topolittle/rx8-coolant-monitor/MECHA/Head_Unit/STEP/Head_Unit_cutting_jig.STEP

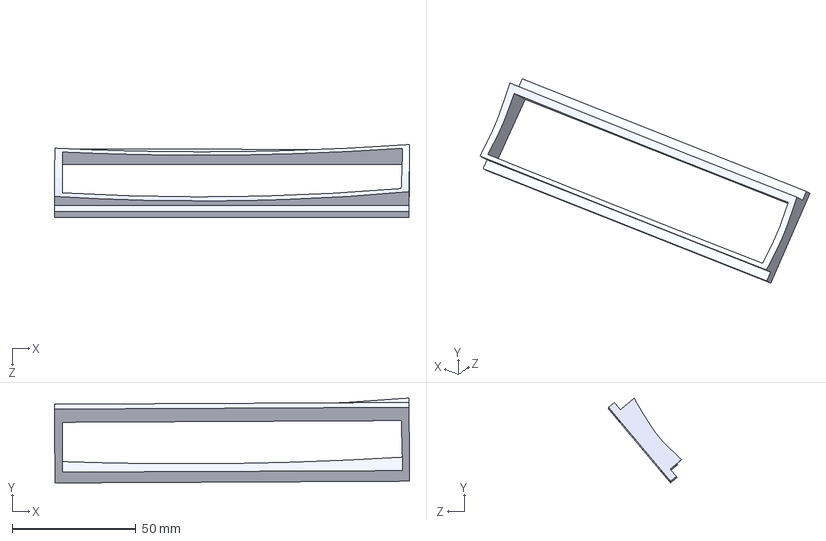
[picture p23: CAD file, 2022-10-16]
MECHA/Head_Unit/STEP/Head_Unit_cutting_jig.STEP
143.4 x 34.3 x 29.4 mm
