topolittle/rx8-coolant-monitor/MECHA/Controller_Enclosure/Solidworks/1723162108.SLDPRT

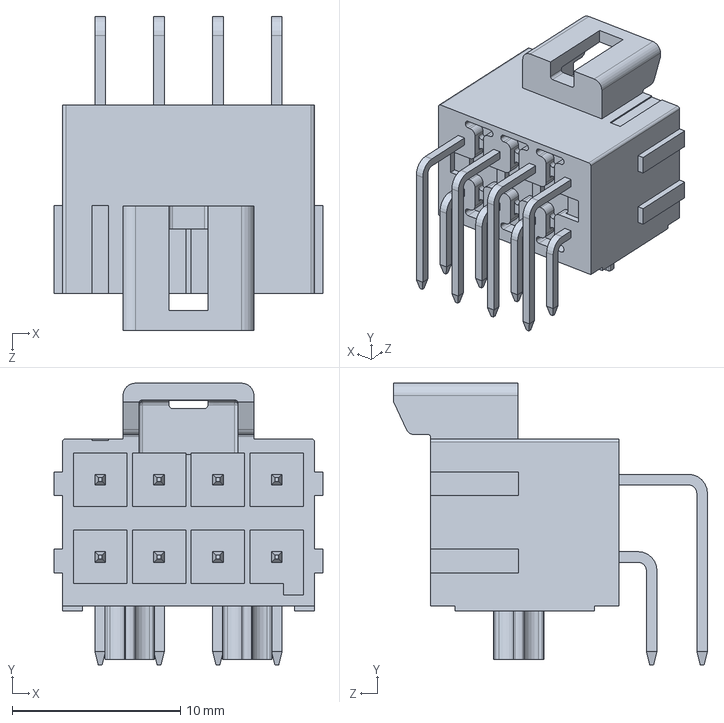
[picture p24: CAD file, 2022-10-16]
MECHA/Controller_Enclosure/Solidworks/1723162108.SLDPRT
16.0 x 16.8 x 18.7 mm
