topolittle/rx8-coolant-monitor/MECHA/Head_Unit/IMAGES/Head_Unit_Assembly_back.PNG

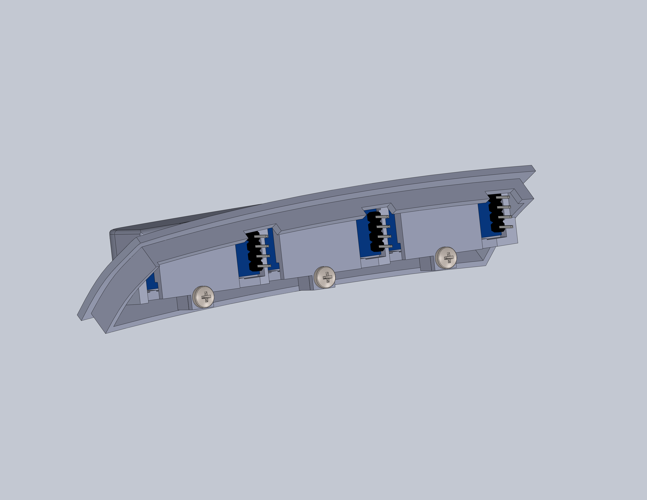
MECHA/Head_Unit/IMAGES/Head_Unit_Assembly_back.PNG
