topolittle/rx8-coolant-monitor/IMAGES/testing.jpg

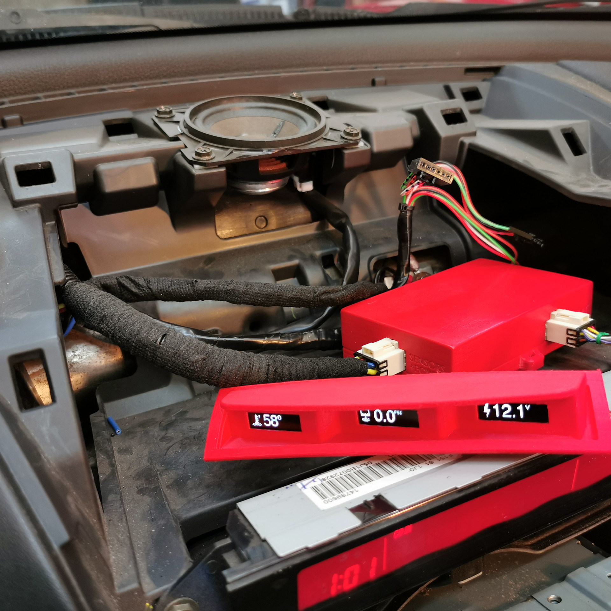
IMAGES/testing.jpg
