topolittle/rx8-coolant-monitor/EMBEDDED/src/coolant_monitor/FreeSans18pt7bNum.h

/* 
 * This is the standard Adafruit FreeSans18pt7b font but without letters and symbols.
 * Only numbers, sing and ponctuation have been keept to save space.
 * The original source code is available here:
 * https://github.com/adafruit/Adafruit-GFX-Library/blob/master/Fonts/FreeSans18pt7b.h
 * The code is distributed under the BSD licence. To comply with the license, a copy of
 * the original license file was retreived and put beside this file under the name
 * 'Copying-Adafruit-GFX-Library.txt'. The file was retreived from the above GitHub
 * repository on the 'master' branch, commit 91d916deeb75263582a2456cb211ebdaf06b840b.
*/

#include <gfxfont.h>

const uint8_t FreeSans18pt7bBitmapsNum[] PROGMEM = {
    0xFF, 0xFF, 0xFF, 0xFF, 0xFF, 0xFF, 0xE9, 0x20, 0x3F, 0xFC, 0xE3, 0xF1,
    0xF8, 0xFC, 0x7E, 0x3F, 0x1F, 0x8E, 0x82, 0x41, 0x00, 0x01, 0xC3, 0x80,
    0x38, 0x70, 0x06, 0x0E, 0x00, 0xC1, 0x80, 0x38, 0x70, 0x07, 0x0E, 0x0F,
    0xFF, 0xF9, 0xFF, 0xFF, 0x3F, 0xFF, 0xE0, 0xE1, 0xC0, 0x1C, 0x38, 0x03,
    0x87, 0x00, 0x70, 0xE0, 0x0C, 0x18, 0x3F, 0xFF, 0xF7, 0xFF, 0xFE, 0xFF,
    0xFF, 0xC1, 0xC3, 0x80, 0x30, 0x60, 0x06, 0x0C, 0x01, 0xC3, 0x80, 0x38,
    0x70, 0x07, 0x0E, 0x00, 0xC1, 0x80, 0x03, 0x00, 0x0F, 0xC0, 0x3F, 0xF0,
    0x3F, 0xF8, 0x7B, 0x3C, 0xF3, 0x1C, 0xE3, 0x0E, 0xE3, 0x0E, 0xE3, 0x0E,
    0xE3, 0x00, 0xE3, 0x00, 0xF3, 0x00, 0x7B, 0x00, 0x7F, 0x80, 0x1F, 0xF0,
    0x07, 0xFC, 0x03, 0x7E, 0x03, 0x0F, 0x03, 0x07, 0xE3, 0x07, 0xE3, 0x07,
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
    {886, 16, 25, 19, 1, -24},  // 0x39 '9'
};

const GFXfont FreeSans18pt7bNum PROGMEM = {(uint8_t *)FreeSans18pt7bBitmapsNum,
                                        (GFXglyph *)FreeSans18pt7bGlyphsNum, 0x20,
                                        0x7E, 42};
